gromain/Keybon/keybon12/bmp.h

// size of BMP are 64x48 px


unsigned char bmp_swap[384];


static const unsigned char PROGMEM bmp_backward[] =
{
  0x00, 0x00, 0x00, 0x00, 0x00, 0x00, 0x00, 0x00, 0x00, 0x00, 0x00, 0x00, 0x00, 0x00, 0x00, 0x00,
  0x00, 0x00, 0x00, 0x00, 0x00, 0x00, 0x00, 0x00, 0x00, 0x00, 0x00, 0x00, 0x00, 0x00, 0x00, 0x00,
  0x38, 0x00, 0x00, 0x00, 0x07, 0x00, 0x00, 0x0e, 0x38, 0x00, 0x00, 0x00, 0x0f, 0x00, 0x00, 0x3e,
  0x38, 0x00, 0x00, 0x00, 0x3f, 0x00, 0x00, 0xfe, 0x38, 0x00, 0x00, 0x00, 0xfc, 0x00, 0x01, 0xf8,
  0x38, 0x00, 0x00, 0x03, 0xf0, 0x00, 0x07, 0xe0, 0x38, 0x00, 0x00, 0x0f, 0xe0, 0x00, 0x1f, 0x80,
  0x38, 0x00, 0x00, 0x3f, 0x80, 0x00, 0x7e, 0x00, 0x38, 0x00, 0x00, 0x7e, 0x00, 0x01, 0xfc, 0x00,
  0x38, 0x00, 0x01, 0xf8, 0x00, 0x07, 0xf0, 0x00, 0x38, 0x00, 0x07, 0xe0, 0x00, 0x1f, 0xc0, 0x00,
  0x38, 0x00, 0x1f, 0x80, 0x00, 0x3f, 0x00, 0x00, 0x38, 0x00, 0x7e, 0x00, 0x00, 0xfc, 0x00, 0x00,
  0x38, 0x01, 0xfc, 0x00, 0x03, 0xf0, 0x00, 0x00, 0x38, 0x03, 0xf0, 0x00, 0x0f, 0xc0, 0x00, 0x00,
  0x38, 0x0f, 0xc0, 0x00, 0x3f, 0x80, 0x00, 0x00, 0x38, 0x3f, 0x00, 0x00, 0xfe, 0x00, 0x00, 0x00,
  0x38, 0xfc, 0x00, 0x01, 0xf8, 0x00, 0x00, 0x00, 0x39, 0xf0, 0x00, 0x07, 0xe0, 0x00, 0x00, 0x00,
  0x3b, 0xe0, 0x00, 0x07, 0x80, 0x00, 0x00, 0x00, 0x3b, 0x80, 0x00, 0x0f, 0x00, 0x00, 0x00, 0x00,
  0x3b, 0x80, 0x00, 0x0f, 0x00, 0x00, 0x00, 0x00, 0x3b, 0xe0, 0x00, 0x07, 0x80, 0x00, 0x00, 0x00,
  0x39, 0xf0, 0x00, 0x07, 0xe0, 0x00, 0x00, 0x00, 0x38, 0xfc, 0x00, 0x03, 0xf8, 0x00, 0x00, 0x00,
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
  0x00, 0x00, 0x00, 0x00, 0x00, 0x00, 0x00, 0x00, 0x00, 0x00, 0x00, 0x00, 0x00, 0x00, 0x00, 0x00,
  0x00, 0x00, 0x00, 0x00, 0x00, 0x00, 0x00, 0x00, 0x00, 0x00, 0x00, 0x00, 0x00, 0x00, 0x00, 0x00,
  0x00, 0x00, 0x00, 0x00, 0x00, 0x00, 0x00, 0x00, 0x00, 0x00, 0x00, 0x00, 0x00, 0x00, 0x00, 0x00
  */
